Gregox273/Embedded-AGC-DSKY-emulator/firmware/embedded_agc.h

///*
// * Embedded AGC
// */
//#ifndef __EMBEDDED_AGC_H__
//#define __EMBEDDED_AGC_H__
//
//#include "ch.h"
//#include "agc_engine.h"
//
//void embedded_agc_init(agc_t *State);
//extern binary_semaphore_t agc_bsem;
//
//#endif /* __EMBEDDED_AGC_H__ */
